cmdc0de/InfinityMirror/firmware/Core/Src/app.h

/*
 * app.h
 *
 *  Created on: Apr 5, 2020
 *      Author: dcomes
 */

#ifndef SRC_APP_H_
#define SRC_APP_H_

#ifdef __cplusplus
extern "C" {
#endif
void initApp();
void run();

#ifdef __cplusplus
}
#endif


#endif /* SRC_APP_H_ */
